arturs-lab/mintz80_main_pcb/img/Rev5_btm.jpg

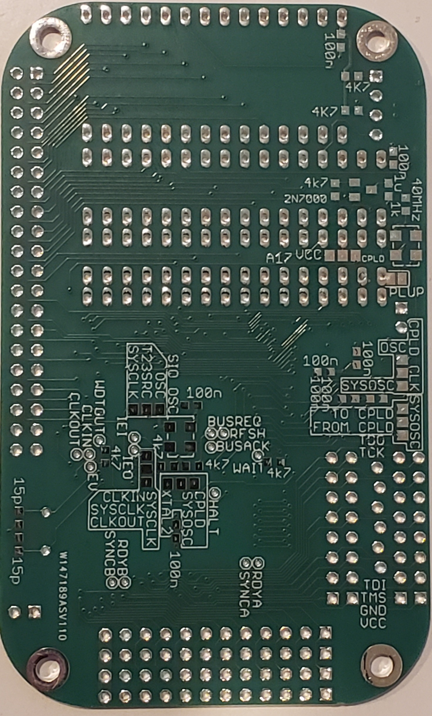
img/Rev5_btm.jpg
